aleppax/AirQualityMesh/casing/development-layout1.jpg

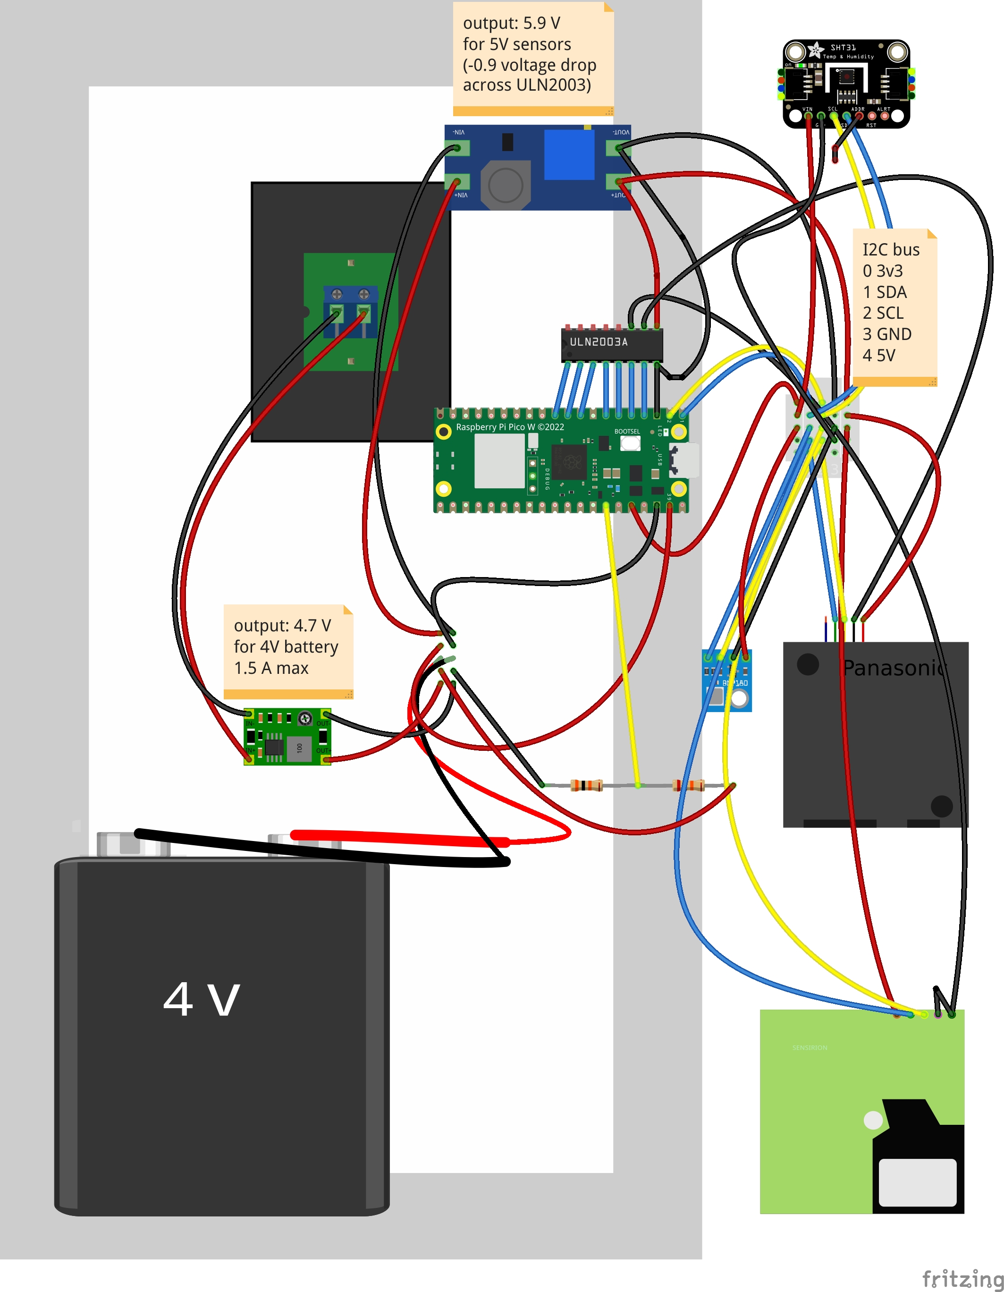
casing/development-layout1.jpg
